orinocoz/All-In-One-Garage-ESP/D1MiniPins.h

#define LED_BUILTIN 2

#define D0 16       //* high on boot, does not have pwm support
#define D1 5
#define D2 4
#define D3 0        //* pull-up, Run/Flash
#define D4 2        //* high on boot, pull-up, LED
#define D5 14
#define D6 12
#define D7 13
#define D8 15       //* pull-down
#define RX 3        //* high on boot
#define TX 1        //* high on boot
